opcow/spinner_control_case/STEP/button-cover.step

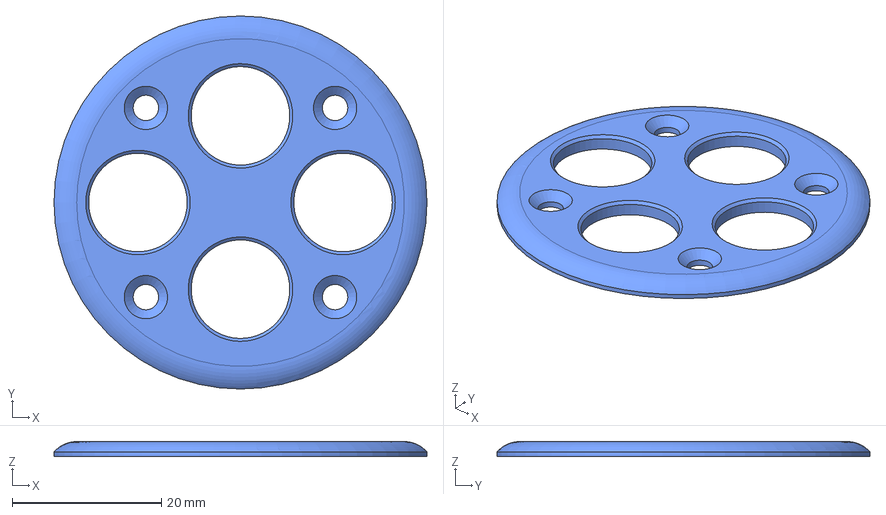
[picture p19: CAD file, 2023-09-02]
STEP/button-cover.step
50.0 x 50.0 x 2.00 mm
