opcow/spinner_control_case/STEP/microswitch-carrier.step

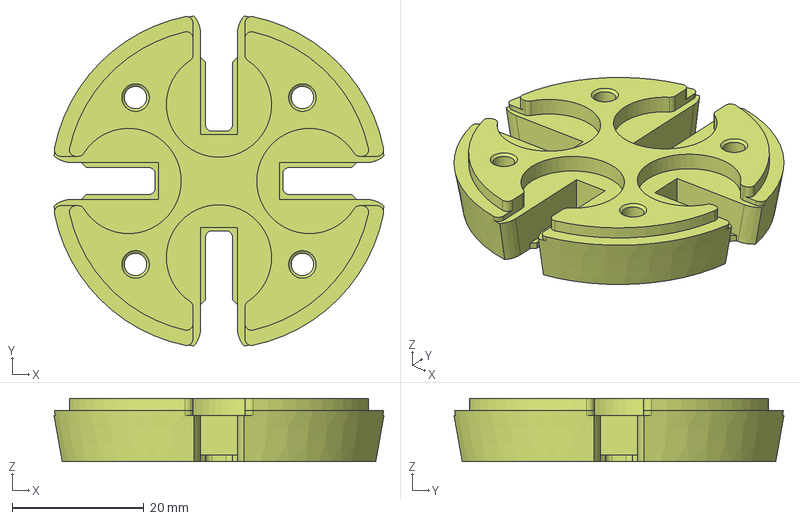
[picture p20: CAD file, 2023-09-02]
STEP/microswitch-carrier.step
50.2 x 50.2 x 9.60 mm
