opcow/spinner_control_case/STEP/top-cover.step

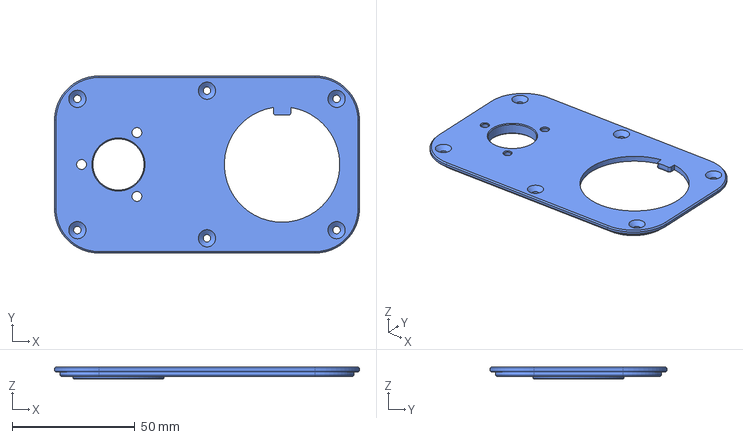
[picture p21: CAD file, 2023-09-02]
STEP/top-cover.step
124.0 x 72.0 x 5.00 mm
