opcow/spinner_control_case/STEP/12mm-button.step

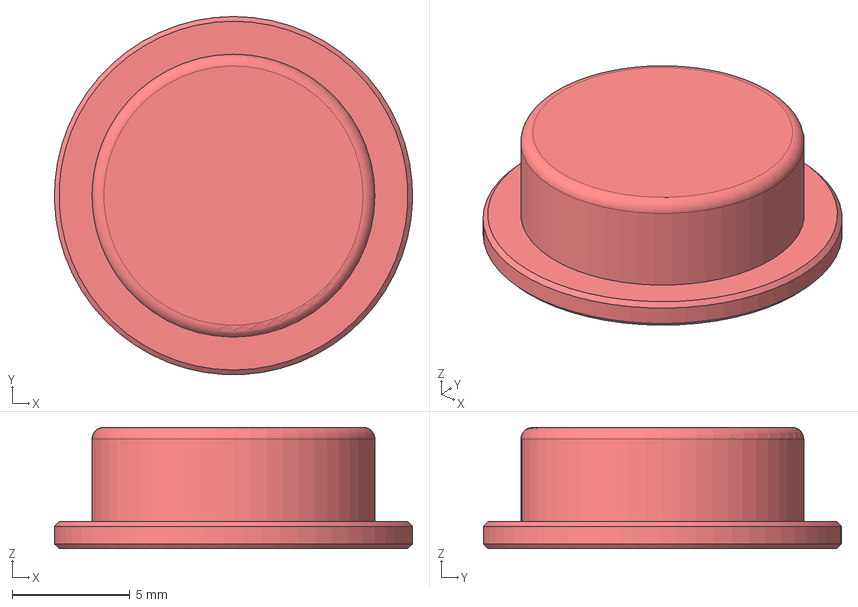
[picture p22: CAD file, 2023-09-02]
STEP/12mm-button.step
15.2 x 15.2 x 5.15 mm
